trek2710/esp32-boat/docs/adr/archive/README.md

# Archived ADRs

ADRs in this folder were **superseded** during round 84 / 85 and no
longer describe how the system behaves today. They are retained here
(rather than deleted) so the reasoning chain that led to the current
design is still readable from git history alone.

| File | Original date | Superseded by |
|---|---|---|
| `0003-udp-multicast-transport.md` | round 81 | [ADR-0010](../0010-unicast-star-ap-relay.md) — unicast star + AP relay |
| `0004-bridge-allow-list.md` | round 82 | [ADR-0011](../0011-safety-boundary-at-wifi-admission.md) — safety moves to WiFi admission |
| `0006-periodic-republish.md` | round 82 | [ADR-0012](../0012-ais-cache-replay.md) — AIS-only cache replay |
| `0008-bench-tx-hosts-softap.md` | round 81 | [ADR-0009](../0009-wifi-role-election.md) — runtime role election |

Active ADRs live in the parent directory. Each archived ADR carries a
"Superseded by …" banner at the top pointing forward.
