trek2710/esp32-boat/docs/hardware/images/esp32c6_components.jpg

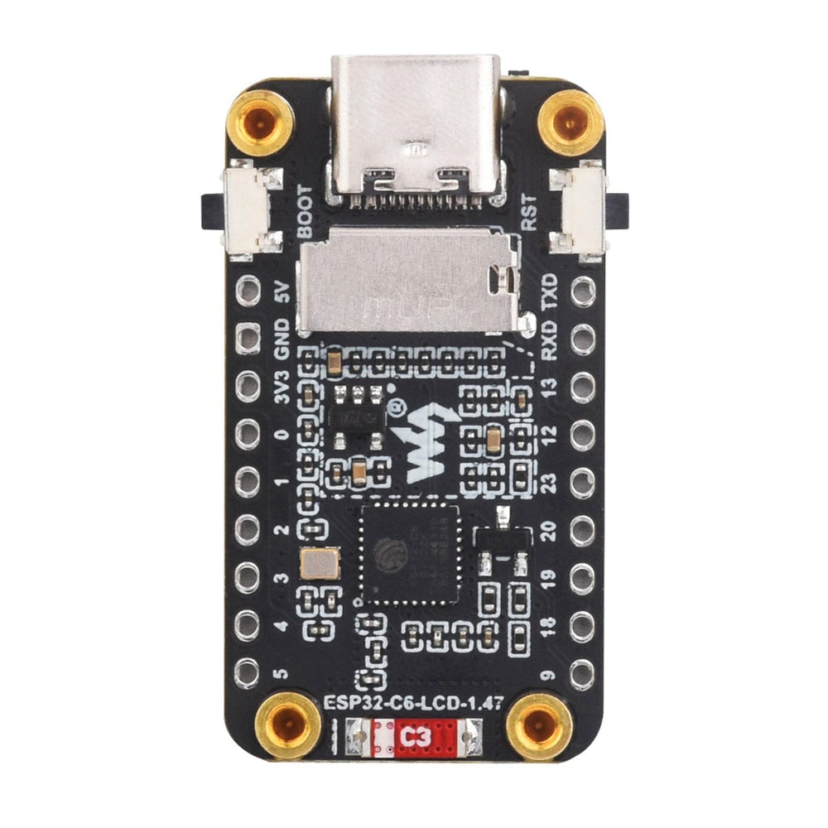
docs/hardware/images/esp32c6_components.jpg
