trek2710/esp32-boat/devices/ais-radar/src/Ble.cpp

#include "Ble.h"

#include <Arduino.h>
#include <NimBLEDevice.h>
#include <cmath>
#include <AisRadarBle.h>
#include <AisFilter.h>
#include "DeviceSettings.h"

namespace ble {
namespace {

NimBLECharacteristic* g_own = nullptr;
NimBLECharacteristic* g_tgt = nullptr;
NimBLECharacteristic* g_set = nullptr;
NimBLECharacteristic* g_log = nullptr;
bool g_connected = false;
uint32_t g_lastLogMs = 0;          // last raw dAISy line — drives the heartbeat bit

void loadSettingsValue() {
    BleSettings s;
    s.range_cap_nm   = devsettings::get().rangeCapNm;
    s.hide_anchored  = devsettings::get().hideAnchored;
    s.depth_thresh_m = devsettings::get().depthThreshM;
    s.chart_layers   = devsettings::get().chartLayers;
    s.test_targets   = devsettings::get().testTargets;
    s.phone_gps      = devsettings::get().phoneGps;
    s.proj_min       = devsettings::get().projMin;
    if (g_set) g_set->setValue((uint8_t*)&s, sizeof(s));
}

class SettingsCb : public NimBLECharacteristicCallbacks {
    void onWrite(NimBLECharacteristic* c) override {
        const std::string v = c->getValue();
        if (v.size() < sizeof(BleSettings)) return;
        BleSettings s;
        memcpy(&s, v.data(), sizeof(s));
        devsettings::set(s.range_cap_nm, s.hide_anchored, s.depth_thresh_m,
                         s.chart_layers, s.test_targets, s.phone_gps, s.proj_min);
        loadSettingsValue();           // echo the clamped/applied value
        if (g_connected) g_set->notify();
    }
};
SettingsCb g_setCb;

HostGps  g_host;
uint32_t g_hostMs = 0;
constexpr uint32_t kHostFreshMs = 30000;   // keep using the phone fix across
                                           // normal GPS update gaps (no bench flip-flop)

double e7d(int32_t v)  { return (v == INT32_MIN) ? NAN : v / 1e7; }
double d10d(int16_t v) { return (v == INT16_MIN) ? NAN : v / 10.0; }

class GpsCb : public NimBLECharacteristicCallbacks {
    void onWrite(NimBLECharacteristic* c) override {
        const std::string v = c->getValue();
        if (v.size() < sizeof(BleHostGps)) return;
        BleHostGps g;
        memcpy(&g, v.data(), sizeof(g));
        g_host.lat    = e7d(g.lat_e7);
        g_host.lon    = e7d(g.lon_e7);
        g_host.cogDeg = d10d(g.cog_deg10);
        g_host.sogKn  = d10d(g.sog_kn10);
        g_hostMs = millis();
    }
};
GpsCb g_gpsCb;

class ServerCb : public NimBLEServerCallbacks {
    void onConnect(NimBLEServer*) override {
        g_connected = true;
        Serial.println("[ble] central connected");
    }
    void onDisconnect(NimBLEServer*) override {
        g_connected = false;
        Serial.println("[ble] central disconnected — re-advertising");
        NimBLEDevice::startAdvertising();
    }
};
ServerCb g_cb;

int32_t e7(double d)   { return (int32_t)llround(d * 1e7); }
int16_t d10(double v)  { return (int16_t)lround(v * 10.0); }

}  // namespace

void begin() {
    NimBLEDevice::init(AISRADAR_BLE_NAME);
    NimBLEDevice::setMTU(247);                  // BleTarget is 38 B → need MTU ≥ 41
    NimBLEDevice::setPower(ESP_PWR_LVL_P3);
    NimBLEServer* srv = NimBLEDevice::createServer();
    srv->setCallbacks(&g_cb);

    NimBLEService* svc = srv->createService(AISRADAR_BLE_SVC_UUID);
    g_own = svc->createCharacteristic(
        AISRADAR_BLE_OWN_UUID, NIMBLE_PROPERTY::NOTIFY | NIMBLE_PROPERTY::READ);
    g_tgt = svc->createCharacteristic(
        AISRADAR_BLE_TGT_UUID, NIMBLE_PROPERTY::NOTIFY | NIMBLE_PROPERTY::READ);
    NimBLECharacteristic* gps = svc->createCharacteristic(
        AISRADAR_BLE_GPS_UUID, NIMBLE_PROPERTY::WRITE | NIMBLE_PROPERTY::WRITE_NR);
    gps->setCallbacks(&g_gpsCb);
    g_set = svc->createCharacteristic(
        AISRADAR_BLE_SET_UUID,
        NIMBLE_PROPERTY::READ | NIMBLE_PROPERTY::WRITE | NIMBLE_PROPERTY::NOTIFY);
    g_set->setCallbacks(&g_setCb);
    g_log = svc->createCharacteristic(
        AISRADAR_BLE_LOG_UUID, NIMBLE_PROPERTY::NOTIFY | NIMBLE_PROPERTY::READ);
    loadSettingsValue();
    svc->start();

    NimBLEAdvertising* adv = NimBLEDevice::getAdvertising();
    adv->addServiceUUID(AISRADAR_BLE_SVC_UUID);
    adv->setName(AISRADAR_BLE_NAME);
    NimBLEDevice::startAdvertising();
    Serial.printf("[ble] advertising as \"%s\"\n", AISRADAR_BLE_NAME);
}

void publish(AisTargetStore& store, double ownLat, double ownLon,
             double ownCogDeg, double ownSogKn, bool haveFix, int threatLevel,
             int batteryPct) {
    if (!g_connected) return;

    AisTarget t[AisTargetStore::CAPACITY];
    const size_t n = store.snapshotByRecency(t, AisTargetStore::CAPACITY);

    BleOwnShip o;
    // Always send the position the radar is centred on (a bench coord when
    // there's no real GPS fix). The flags bit, not a sentinel, marks whether
    // it's a real fix — so the central can still place targets either way.
    o.lat_e7    = e7(ownLat);
    o.lon_e7    = e7(ownLon);
    o.cog_deg10 = std::isnan(ownCogDeg) ? INT16_MIN : d10(ownCogDeg);
    o.sog_kn10  = std::isnan(ownSogKn) ? INT16_MIN : d10(ownSogKn);
    o.flags     = (haveFix ? 0x01 : 0x00)
                | (uint8_t)((threatLevel & 0x03) << 1)
                | ((g_lastLogMs && millis() - g_lastLogMs < 10000) ? 0x08 : 0x00);
    o.targets   = (uint8_t)n;
    o.battery   = (batteryPct < 0 || batteryPct > 100) ? 255 : (uint8_t)batteryPct;
    g_own->setValue((uint8_t*)&o, sizeof(o));
    g_own->notify();

    const uint32_t now = millis();
    for (size_t i = 0; i < n; ++i) {
        const bool hasPos = (t[i].lat_deg != 0.0 || t[i].lon_deg != 0.0);
        if (hasPos) {
            // same range/anchored filter the radar uses, so the app agrees
            const double d2r = 0.017453292519943295;
            const double phi1 = ownLat * d2r, phi2 = t[i].lat_deg * d2r;
            const double dphi = (t[i].lat_deg - ownLat) * d2r;
            const double dlam = (t[i].lon_deg - ownLon) * d2r;
            const double a = sin(dphi / 2) * sin(dphi / 2)
                           + cos(phi1) * cos(phi2) * sin(dlam / 2) * sin(dlam / 2);
            const double rngNm = 3440.065 * 2 * atan2(sqrt(a), sqrt(1 - a));
            if (aisfilter::hidden(t[i].nav_status, rngNm,
                                  devsettings::get().rangeCapNm,
                                  devsettings::get().hideAnchored)) continue;
        }
        BleTarget bt;
        bt.mmsi      = t[i].mmsi;
        bt.lat_e7    = hasPos ? e7(t[i].lat_deg) : INT32_MIN;
        bt.lon_e7    = hasPos ? e7(t[i].lon_deg) : INT32_MIN;
        bt.sog_kn10  = (t[i].sog_kn  >= 0) ? d10(t[i].sog_kn)  : INT16_MIN;
        bt.cog_deg10 = (t[i].cog_deg >= 0) ? d10(t[i].cog_deg) : INT16_MIN;
        bt.ship_type = t[i].vessel_type;
        const uint32_t age = (now - t[i].last_seen_ms) / 1000;
        bt.age_s     = age > 255 ? 255 : (uint8_t)age;
        memcpy(bt.name, t[i].name, sizeof(bt.name));   // 20 of the 21 NUL-padded chars
        g_tgt->setValue((uint8_t*)&bt, sizeof(bt));
        g_tgt->notify();
        delay(6);   // small gap so back-to-back notifies aren't dropped
    }
}

bool connected() { return g_connected; }

void logLine(const char* s) {
    g_lastLogMs = millis();                  // heartbeat, even if no one's listening
    if (g_connected && g_log) {
        g_log->setValue((uint8_t*)s, strlen(s));
        g_log->notify();
    }
}

bool hostGps(HostGps* out) {
    if (g_hostMs == 0 || (millis() - g_hostMs) > kHostFreshMs) return false;
    *out = g_host;
    return true;
}

}  // namespace ble
